74hc595/68k-nano/code/serload.py

#!/usr/bin/env python3

# Very basic serial loader.
# Does no checking/verification that the upload succeeded
# Code is always loaded into the same location in RAM. (APPMEMSTART)
#
# protocol is:
# - host (this script) sends break condition
# - target (the board) replies with ASCII U
# - host sends entire binary image
# - host sends break condition
# - target reboots

import serial
import sys
import time

BAUD = 57600

if len(sys.argv) != 3:
  print('usage: serload.py <binfile> <port>')
  sys.exit(1)

with open(sys.argv[1], 'rb') as infile:
  ser = serial.Serial(sys.argv[2], BAUD, timeout=1)
  # enter loader
  ser.send_break()
  # wait for acknowledge
  ack = ser.read(1)
  if ack != b'U':
    raise IOError('device did not acknowledge')
  # write bytes
  ser.write(infile.read())
  ser.flush()
  # additional delay sometimes required when sending short files
  # on macOS (dee to closing the serial port too soon?
  time.sleep(1)
  # send a break to finish
  ser.send_break()
